casartar/Tangara-Workshop/Pictures/20241209_231042.jpg

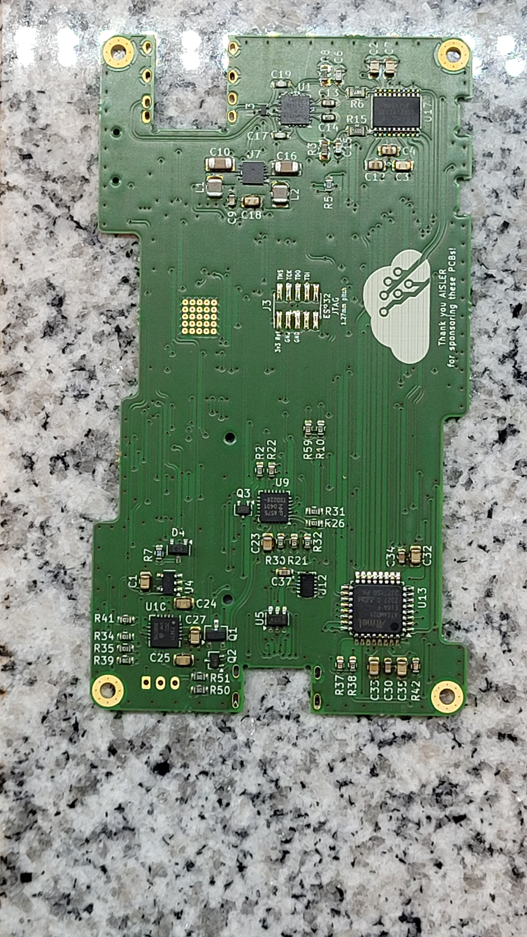
Pictures/20241209_231042.jpg
