casartar/Tangara-Workshop/Pictures/20241209_231124.jpg

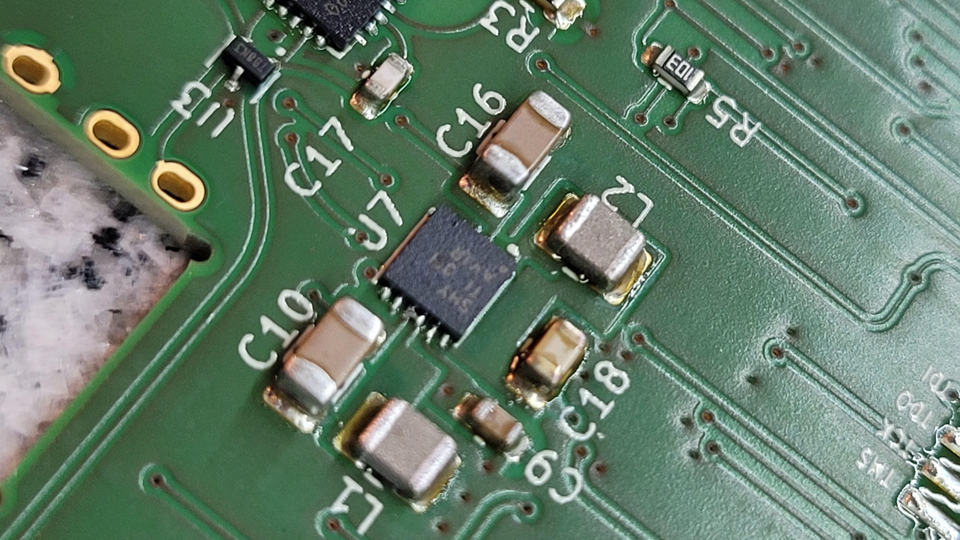
Pictures/20241209_231124.jpg
