casartar/Tangara-Workshop/Pictures/20241209_231136.jpg

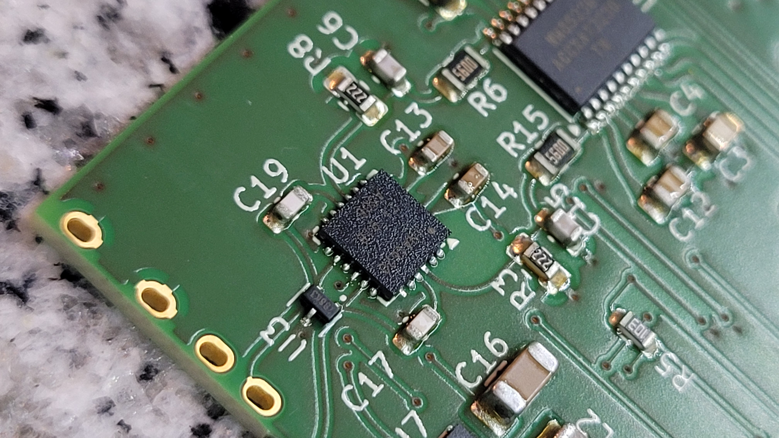
Pictures/20241209_231136.jpg
