casartar/Tangara-Workshop/Pictures/20241209_231150.jpg

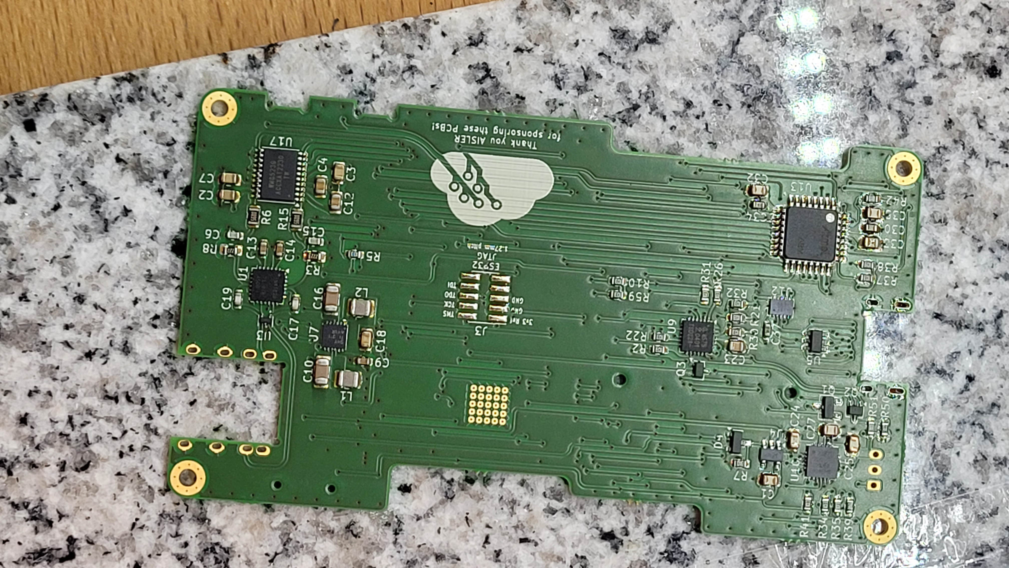
Pictures/20241209_231150.jpg
