casartar/Tangara-Workshop/Pictures/20241209_231156.jpg

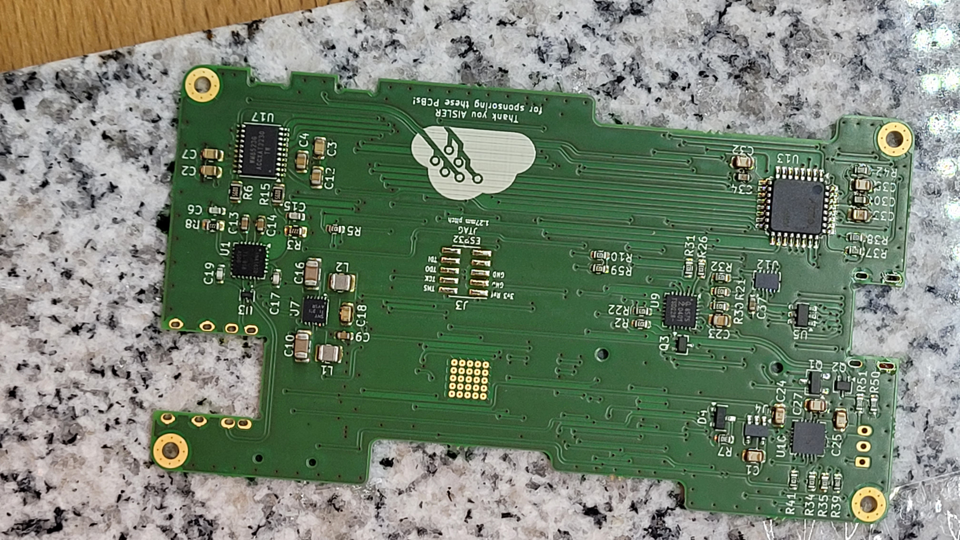
Pictures/20241209_231156.jpg
