casartar/Tangara-Workshop/Pictures/20241209_231208.jpg

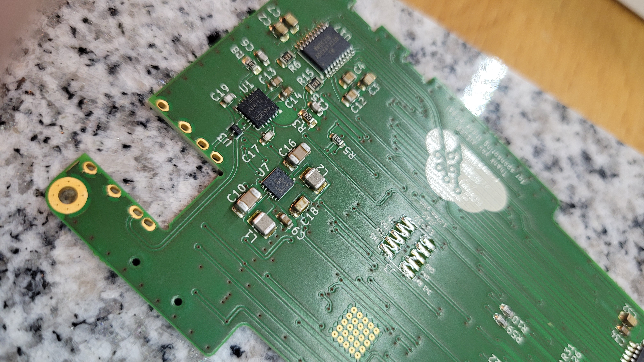
Pictures/20241209_231208.jpg
