casartar/Tangara-Workshop/Pictures/20241209_231745.jpg

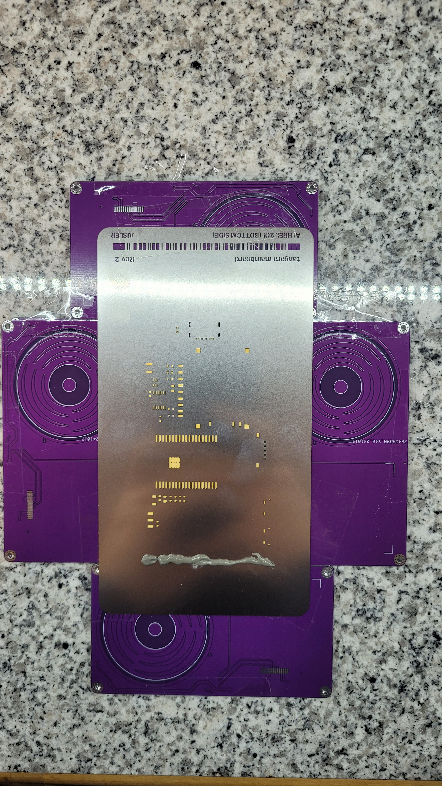
Pictures/20241209_231745.jpg
