casartar/Tangara-Workshop/Pictures/20241209_231748.jpg

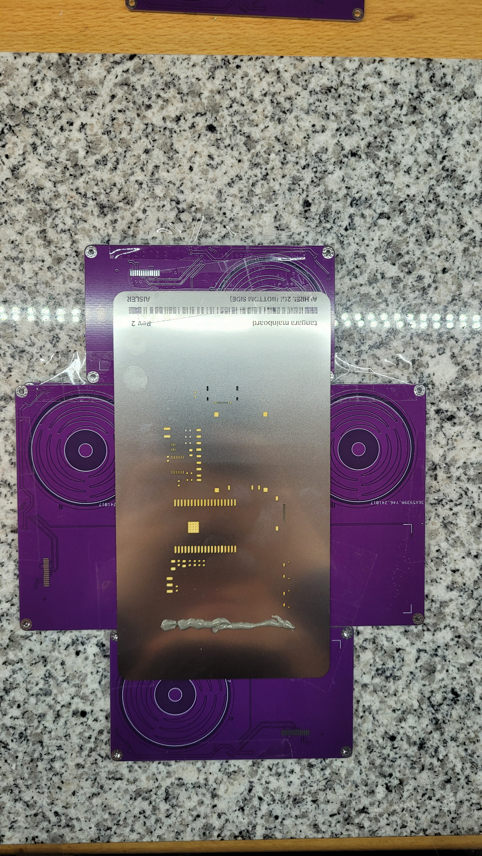
Pictures/20241209_231748.jpg
