casartar/Tangara-Workshop/Pictures/20241209_232118.jpg

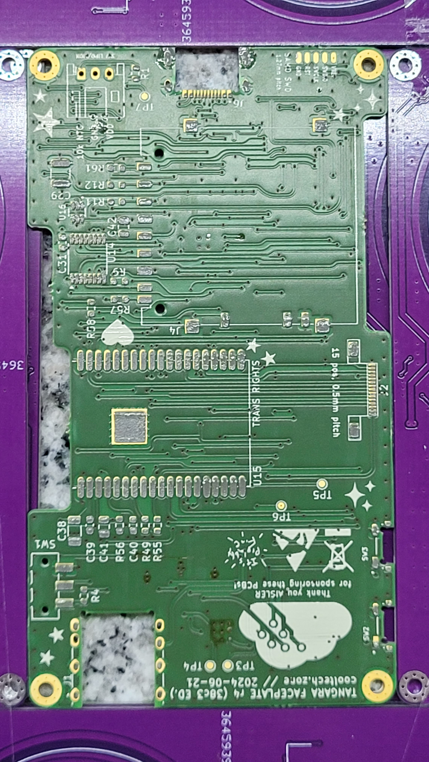
Pictures/20241209_232118.jpg
