casartar/Tangara-Workshop/Pictures/20241209_232123.jpg

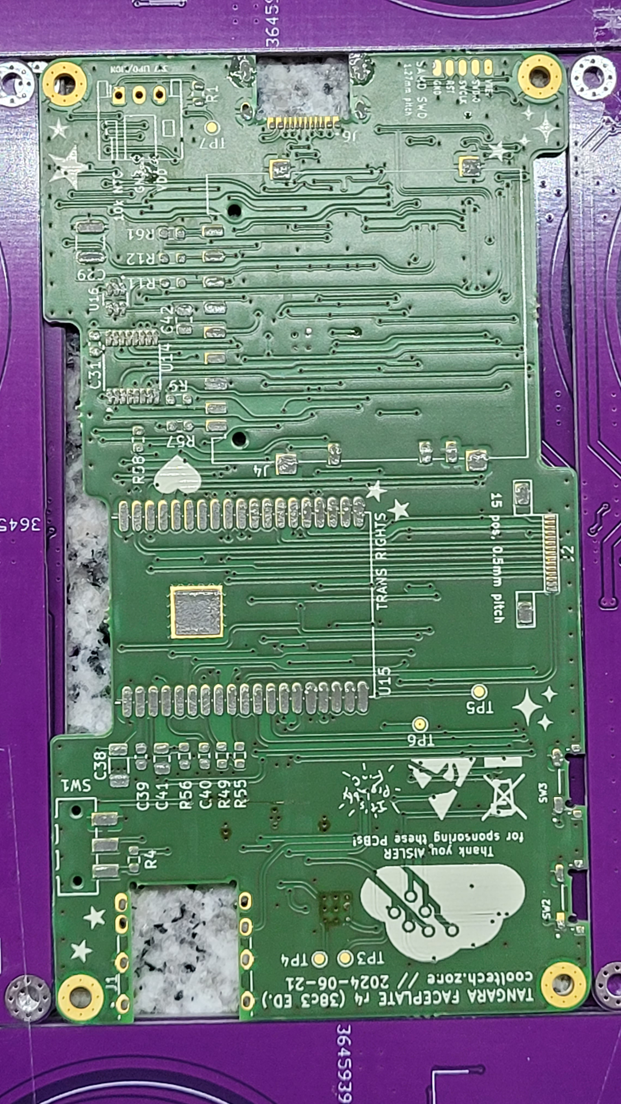
Pictures/20241209_232123.jpg
