casartar/Tangara-Workshop/Pictures/20241209_232130.jpg

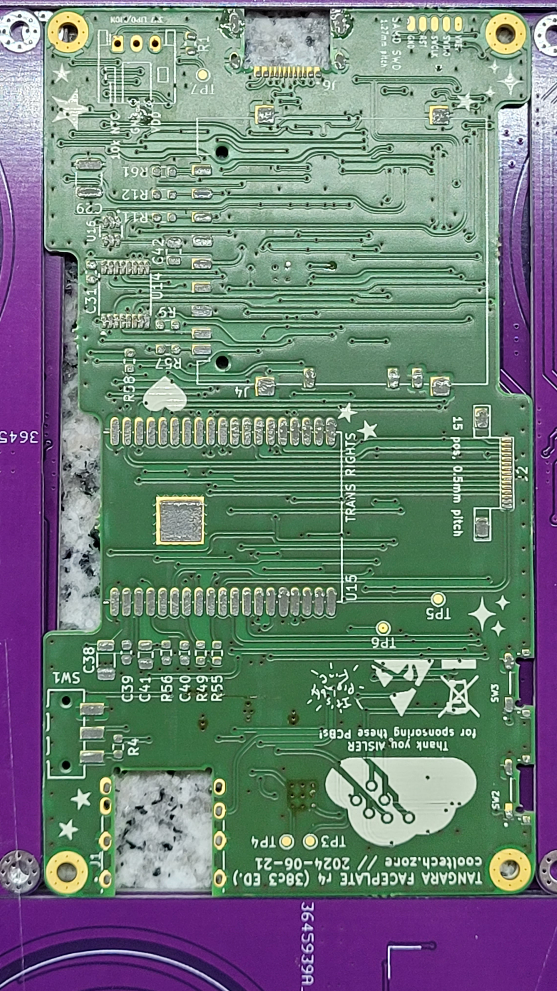
Pictures/20241209_232130.jpg
