casartar/Tangara-Workshop/Pictures/20241209_233654.jpg

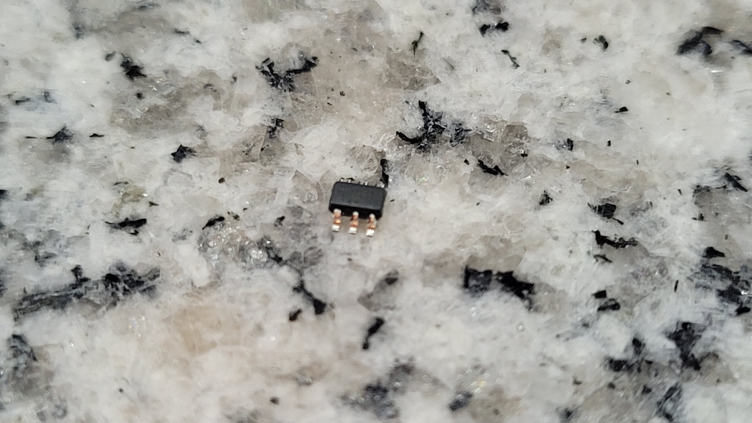
Pictures/20241209_233654.jpg
