casartar/Tangara-Workshop/Pictures/20241209_233658.jpg

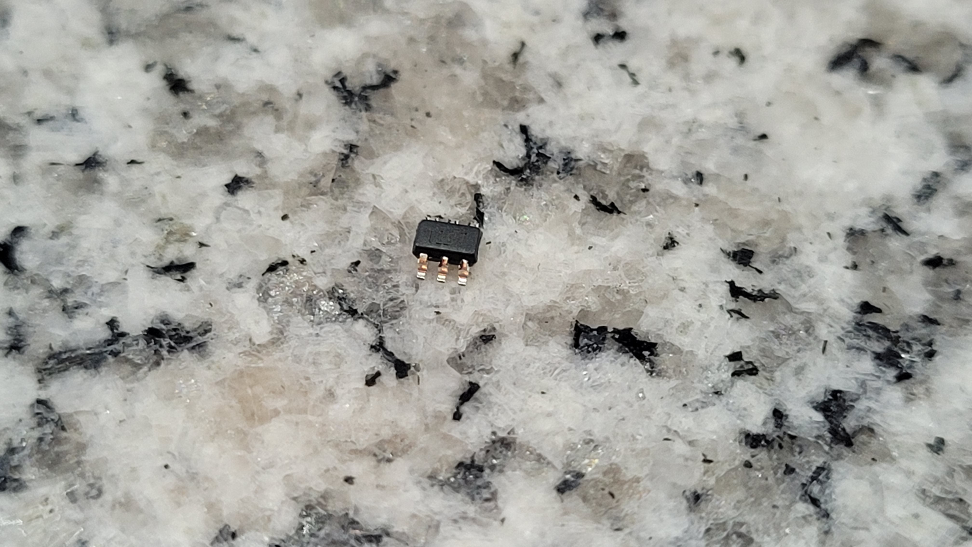
Pictures/20241209_233658.jpg
