casartar/Tangara-Workshop/Pictures/20241209_234436.jpg

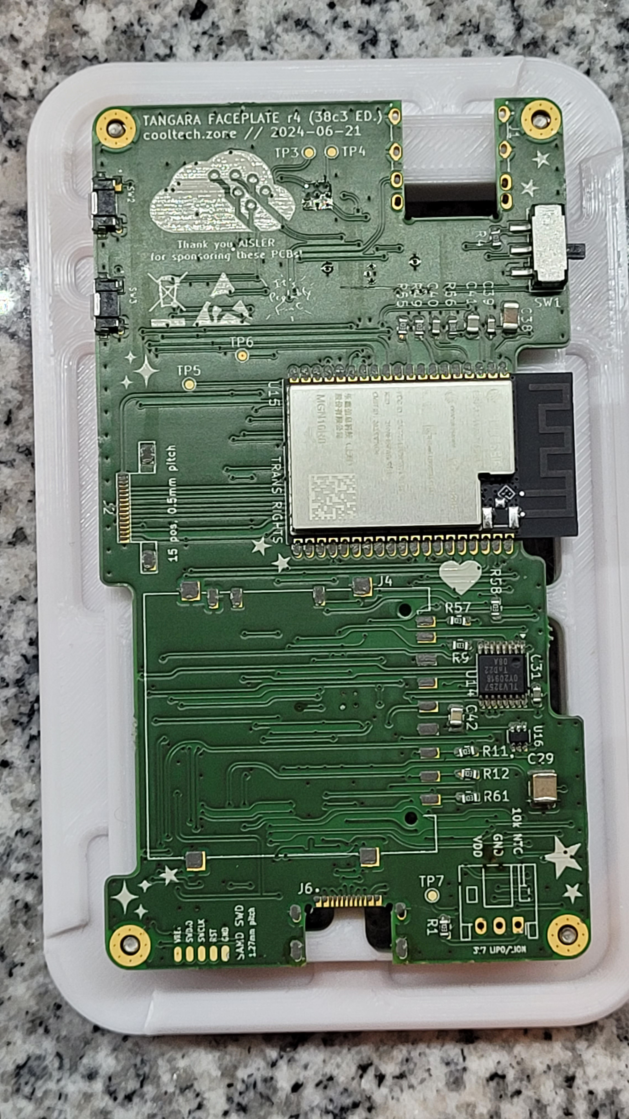
Pictures/20241209_234436.jpg
