casartar/Tangara-Workshop/Pictures/20241209_234439.jpg

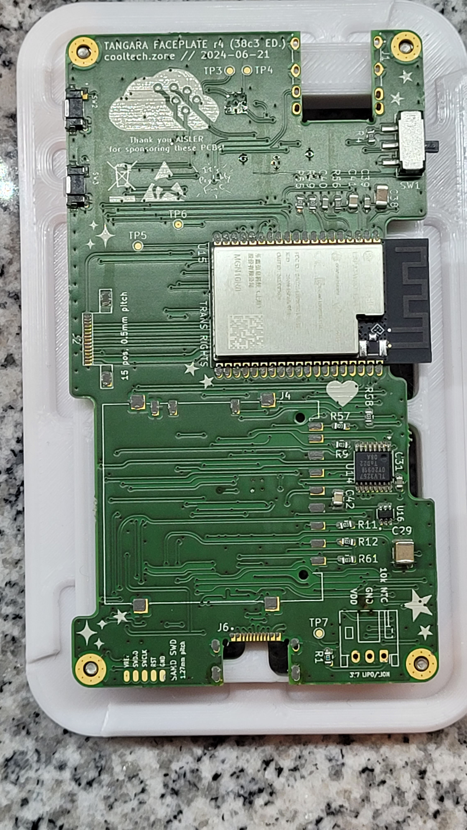
Pictures/20241209_234439.jpg
