casartar/Tangara-Workshop/Pictures/20241209_234729.jpg

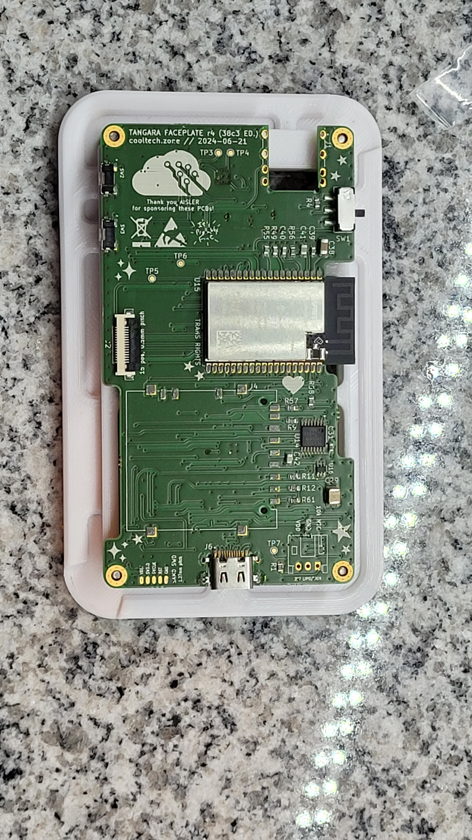
Pictures/20241209_234729.jpg
