casartar/Tangara-Workshop/Pictures/20241209_234736.jpg

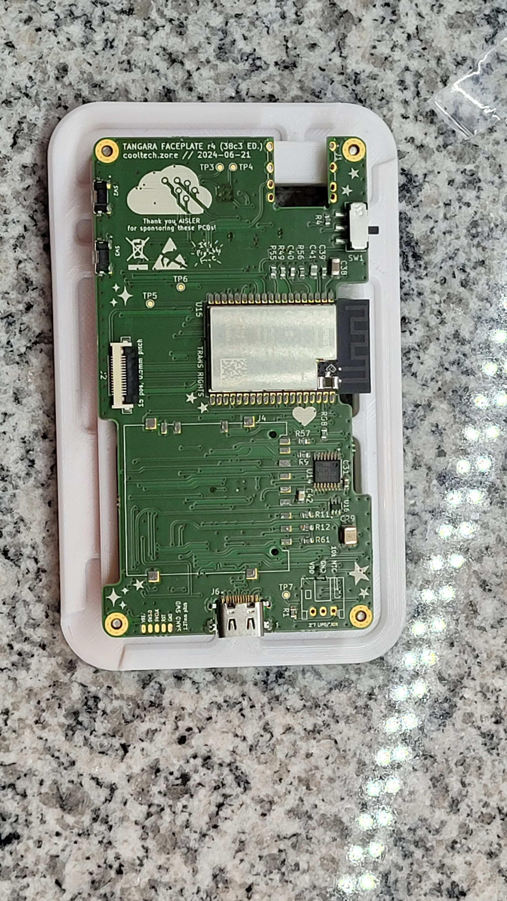
Pictures/20241209_234736.jpg
