casartar/Tangara-Workshop/Pictures/20241209_234742.jpg

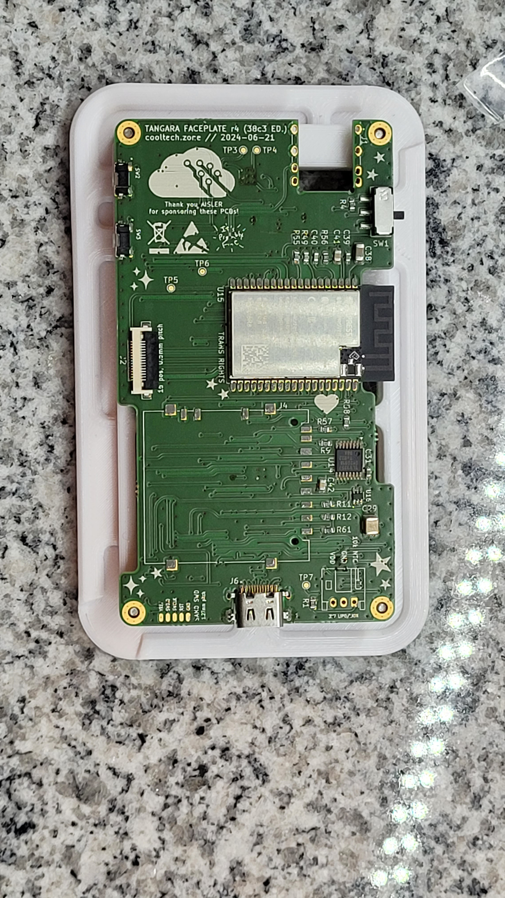
Pictures/20241209_234742.jpg
