casartar/Tangara-Workshop/Pictures/20241210_191028.jpg

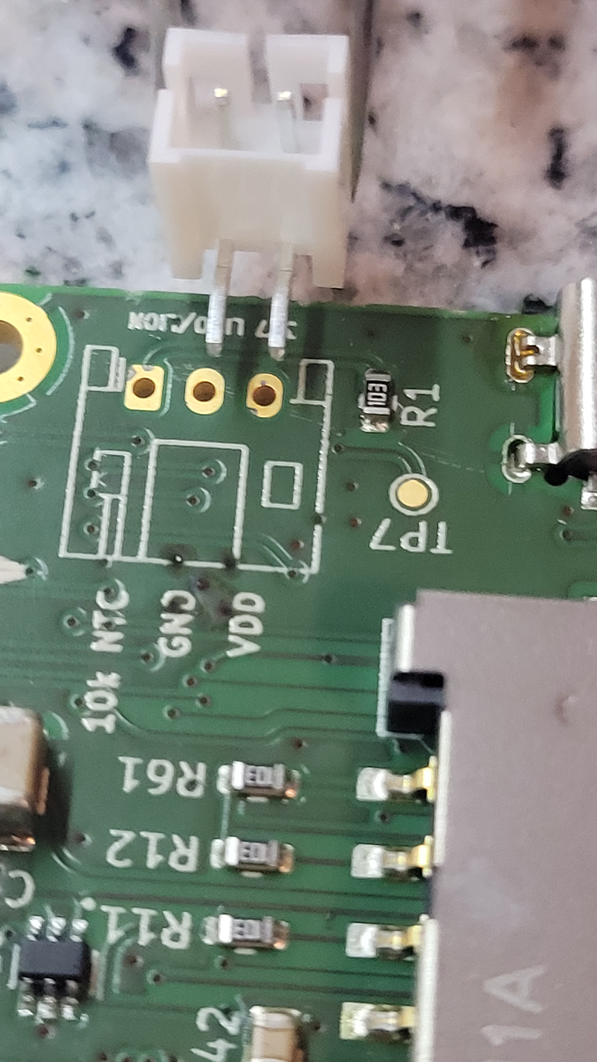
Pictures/20241210_191028.jpg
