casartar/Tangara-Workshop/Pictures/20241210_192213.jpg

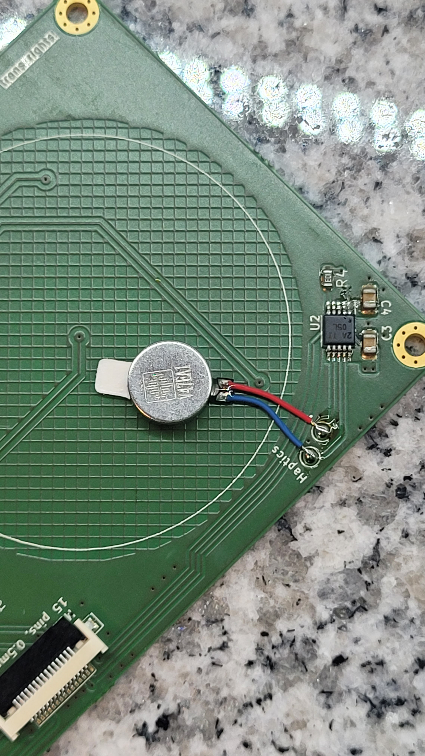
Pictures/20241210_192213.jpg
