casartar/Tangara-Workshop/Pictures/20241210_192219.jpg

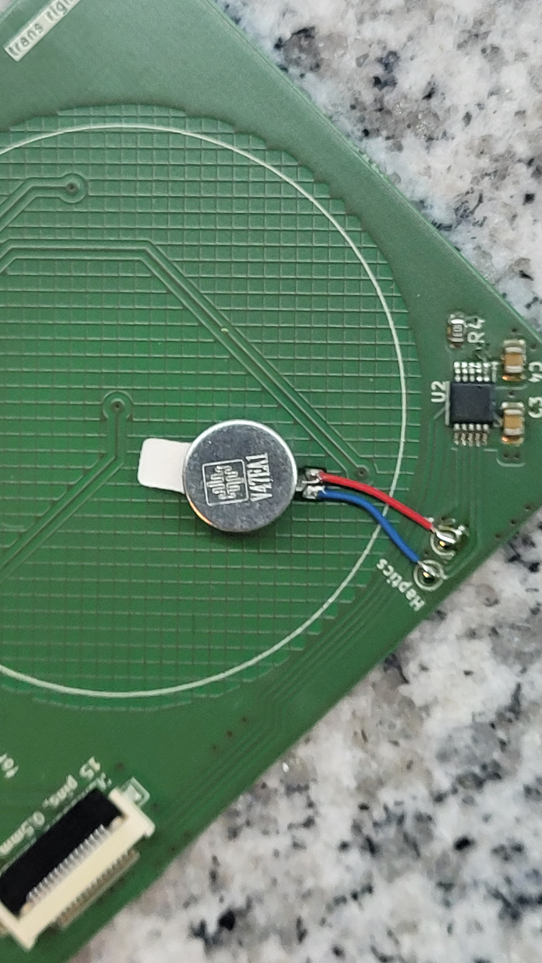
Pictures/20241210_192219.jpg
