casartar/Tangara-Workshop/Pictures/20241210_192222.jpg

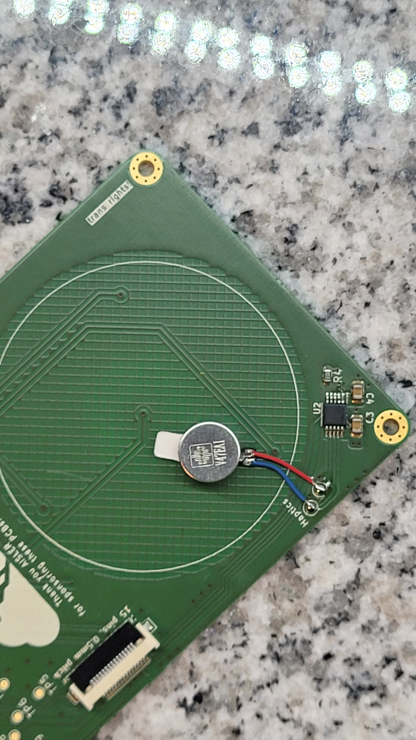
Pictures/20241210_192222.jpg
