casartar/Tangara-Workshop/Pictures/_internal1.jpg

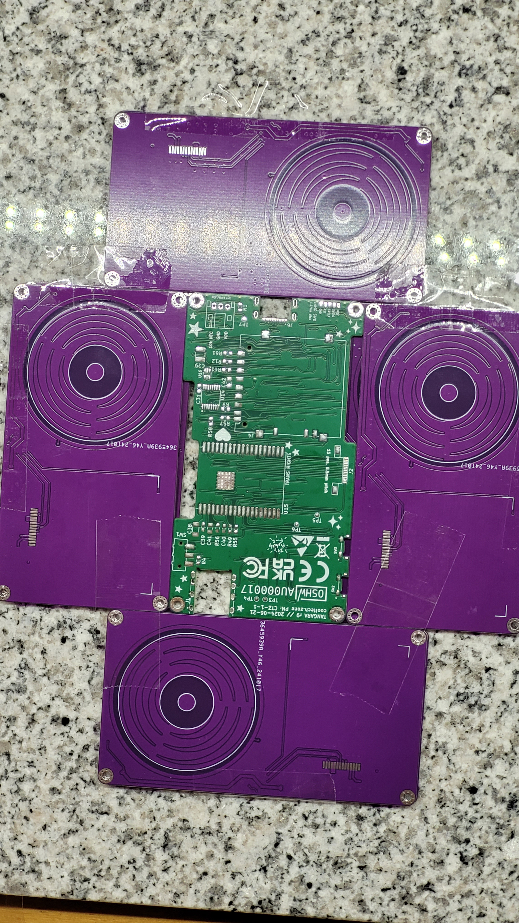
Pictures/_internal1.jpg
