casartar/Tangara-Workshop/Pictures/_internal2.jpg

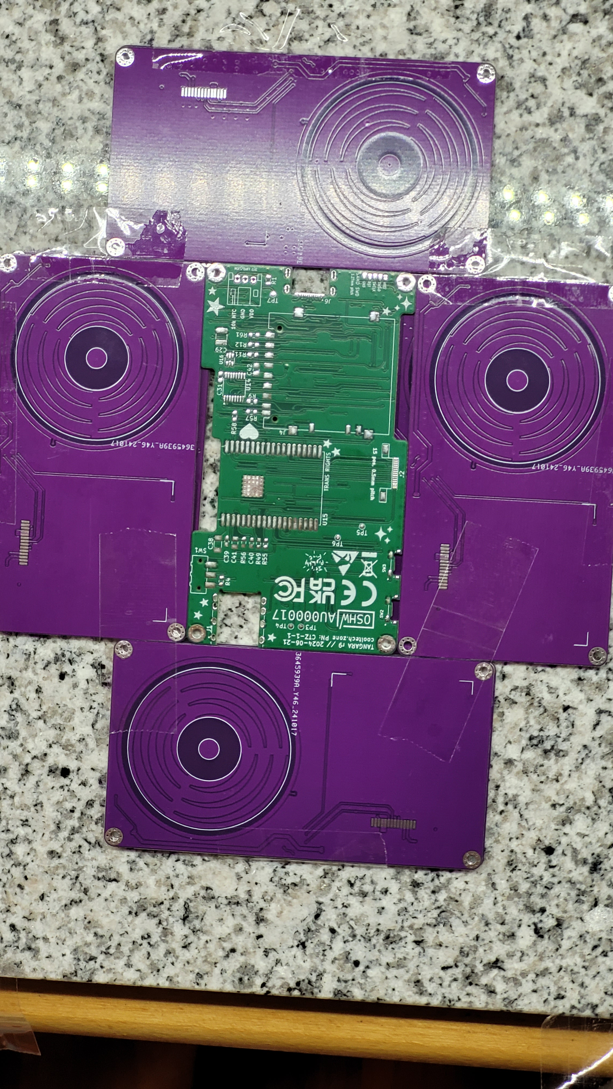
Pictures/_internal2.jpg
