casartar/Tangara-Workshop/Pictures/TPS22948.png

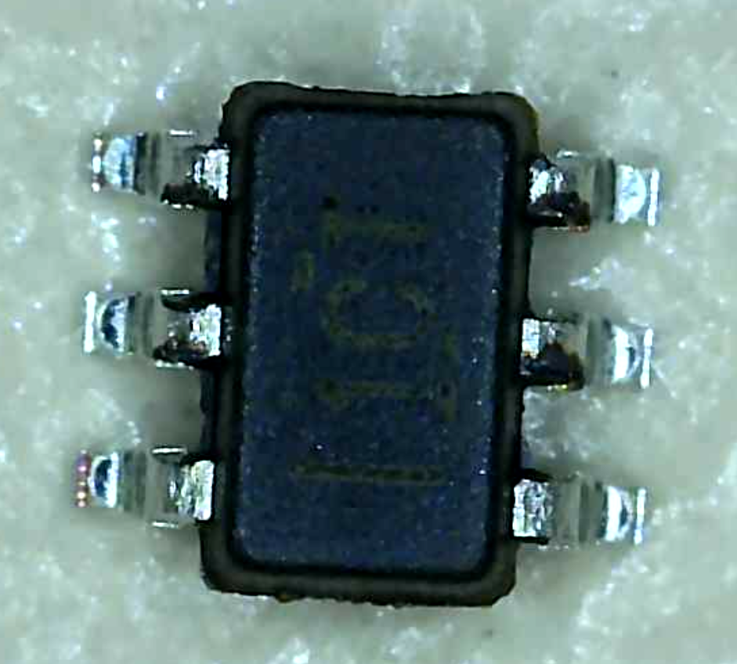
Pictures/TPS22948.png
