casartar/Tangara-Workshop/Pictures/Assembly7_alt.jpg

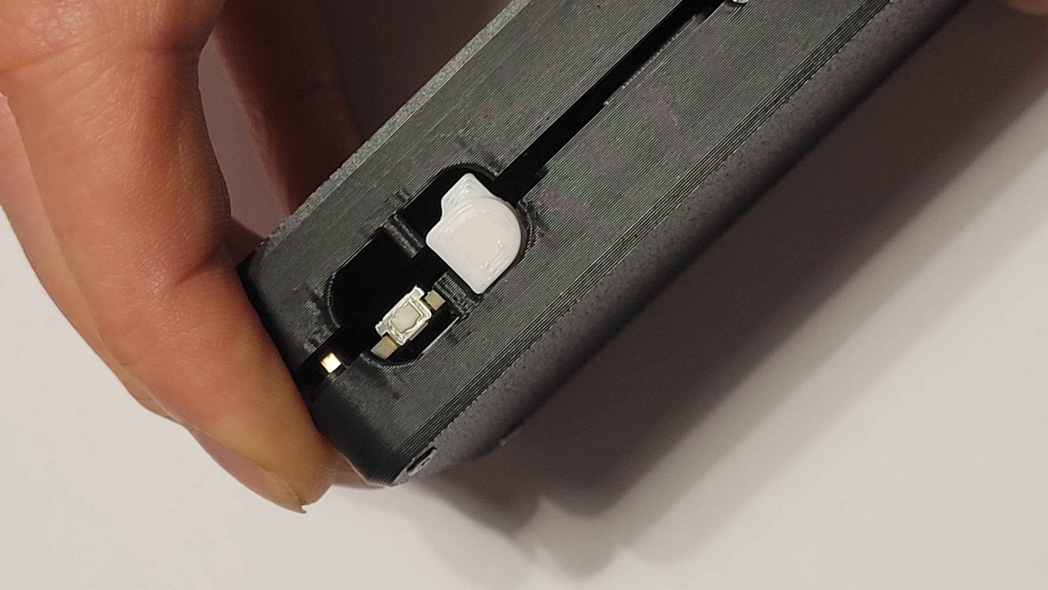
Pictures/Assembly7_alt.jpg
